de1m/co2-meter-mqtt/firmware/user/wifi.h

/*
 * wifi.h
 *
 *  Created on: Dec 30, 2014
 *      Author: Minh
 */

#ifndef USER_WIFI_H_
#define USER_WIFI_H_
#include "os_type.h"
typedef void (*WifiCallback)(uint8_t);
void ICACHE_FLASH_ATTR WIFI_Connect(WifiCallback cb);
unsigned int ICACHE_FLASH_ATTR strintIPtoInt (char *ip, int *ipr);
#endif /* USER_WIFI_H_ */
